alljiang/Lightsaber/Firmware/VWare/PLL.c

// PLL.c
// Runs on LM4F120/TM4C123
// A software function to change the bus frequency using the PLL.
// Daniel Valvano
// 1/17/2020

/* This example accompanies the book
   "Embedded Systems: Real Time Interfacing to Arm Cortex M Microcontrollers",
   ISBN: 978-1463590154, Jonathan Valvano, copyright (c) 2017
   Program 2.10, Figure 2.37

 Copyright 2018 by Jonathan W. Valvano, valvano@mail.utexas.edu
    You may use, edit, run or distribute this file
    as long as the above copyright notice remains
 THIS SOFTWARE IS PROVIDED "AS IS".  NO WARRANTIES, WHETHER EXPRESS, IMPLIED
 OR STATUTORY, INCLUDING, BUT NOT LIMITED TO, IMPLIED WARRANTIES OF
 MERCHANTABILITY AND FITNESS FOR A PARTICULAR PURPOSE APPLY TO THIS SOFTWARE.
 VALVANO SHALL NOT, IN ANY CIRCUMSTANCES, BE LIABLE FOR SPECIAL, INCIDENTAL,
 OR CONSEQUENTIAL DAMAGES, FOR ANY REASON WHATSOEVER.
 For more information about my classes, my research, and my books, see
 http://users.ece.utexas.edu/~valvano/
 */
 
#include <PLL.h>
#include <stdint.h>
#include "inc/tm4c123gh6pm.h"

// The #define statement SYSDIV2 in PLL.h
// initializes the PLL to the desired frequency.

// bus frequency is 400MHz/(SYSDIV2+1) = 400MHz/(7+1) = 50 MHz
// see the table at the end of this file

#define SYSCTL_RIS_PLLLRIS      0x00000040  // PLL Lock Raw Interrupt Status
#define SYSCTL_RCC_XTAL_M       0x000007C0  // Crystal Value
#define SYSCTL_RCC_XTAL_6MHZ    0x000002C0  // 6 MHz Crystal
#define SYSCTL_RCC_XTAL_8MHZ    0x00000380  // 8 MHz Crystal
#define SYSCTL_RCC_XTAL_16MHZ   0x00000540  // 16 MHz Crystal
#define SYSCTL_RCC2_USERCC2     0x80000000  // Use RCC2
#define SYSCTL_RCC2_DIV400      0x40000000  // Divide PLL as 400 MHz vs. 200
                                            // MHz
#define SYSCTL_RCC2_SYSDIV2_M   0x1F800000  // System Clock Divisor 2
#define SYSCTL_RCC2_SYSDIV2LSB  0x00400000  // Additional LSB for SYSDIV2
#define SYSCTL_RCC2_PWRDN2      0x00002000  // Power-Down PLL 2
#define SYSCTL_RCC2_BYPASS2     0x00000800  // PLL Bypass 2
#define SYSCTL_RCC2_OSCSRC2_M   0x00000070  // Oscillator Source 2
#define SYSCTL_RCC2_OSCSRC2_MO  0x00000000  // MOSC

// configure the system to get its clock from the PLL
// SYSDIV = 400/freq -1
// bus frequency is 400MHz/(SYSDIV+1)
void PLL_Init(uint32_t freq){
  // 0) configure the system to use RCC2 for advanced features
  //    such as 400 MHz PLL and non-integer System Clock Divisor
  SYSCTL_RCC2_R |= SYSCTL_RCC2_USERCC2;
  // 1) bypass PLL while initializing
  SYSCTL_RCC2_R |= SYSCTL_RCC2_BYPASS2;
  // 2) select the crystal value and oscillator source
  SYSCTL_RCC_R &= ~SYSCTL_RCC_XTAL_M;   // clear XTAL field
  SYSCTL_RCC_R += SYSCTL_RCC_XTAL_16MHZ;// configure for 16 MHz crystal
  SYSCTL_RCC2_R &= ~SYSCTL_RCC2_OSCSRC2_M;// clear oscillator source field
  SYSCTL_RCC2_R += SYSCTL_RCC2_OSCSRC2_MO;// configure for main oscillator source
  // 3) activate PLL by clearing PWRDN
  SYSCTL_RCC2_R &= ~SYSCTL_RCC2_PWRDN2;
  // 4) set the desired system divider and the system divider least significant bit
  SYSCTL_RCC2_R |= SYSCTL_RCC2_DIV400;  // use 400 MHz PLL
  SYSCTL_RCC2_R = (SYSCTL_RCC2_R&~0x1FC00000) // clear system clock divider field
                  + (freq<<22);      // configure for 80 MHz clock
  // 5) wait for the PLL to lock by polling PLLLRIS
  while((SYSCTL_RIS_R&SYSCTL_RIS_PLLLRIS)==0){};
  // 6) enable use of PLL by clearing BYPASS
  SYSCTL_RCC2_R &= ~SYSCTL_RCC2_BYPASS2;
}


/*
SYSDIV2  Divisor  Clock (MHz)
 0        1       reserved
 1        2       reserved
 2        3       reserved
 3        4       reserved
 4        5       80.000
 5        6       66.667
 6        7       reserved
 7        8       50.000
 8        9       44.444
 9        10      40.000
 10       11      36.364
 11       12      33.333
 12       13      30.769
 13       14      28.571
 14       15      26.667
 15       16      25.000
 16       17      23.529
 17       18      22.222
 18       19      21.053
 19       20      20.000
 20       21      19.048
 21       22      18.182
 22       23      17.391
 23       24      16.667
 24       25      16.000
 25       26      15.385
 26       27      14.815
 27       28      14.286
 28       29      13.793
 29       30      13.333
 30       31      12.903
 31       32      12.500
 32       33      12.121
 33       34      11.765
 34       35      11.429
 35       36      11.111
 36       37      10.811
 37       38      10.526
 38       39      10.256
 39       40      10.000
 40       41      9.756
 41       42      9.524
 42       43      9.302
 43       44      9.091
 44       45      8.889
 45       46      8.696
 46       47      8.511
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
*/
