alljiang/Lightsaber/Firmware/OTFConfig.h

/*
 * OTFConfig.h
 *
 *  Created on: May 1, 2021
 *      Author: Allen
 */

#ifndef OTFCONFIG_H_
#define OTFCONFIG_H_

extern volatile uint8_t primaryR;
extern volatile uint8_t primaryG;
extern volatile uint8_t primaryB;
extern volatile uint8_t secondaryR;
extern volatile uint8_t secondaryG;
extern volatile uint8_t secondaryB;

extern volatile uint8_t fontIndex;
extern volatile uint8_t bladeEffectIndex;

#endif /* OTFCONFIG_H_ */
